slomkowski/octoglow/software/octoglowd2/src/main/kotlin/eu/slomkowski/octoglow/octoglowd/controller/FrontDisplayController.kt

package eu.slomkowski.octoglow.octoglowd.controller

import eu.slomkowski.octoglow.octoglowd.hardware.Hardware
import eu.slomkowski.octoglow.octoglowd.view.FrontDisplayView
import kotlinx.coroutines.channels.ticker
import kotlinx.coroutines.coroutineScope
import kotlinx.coroutines.launch
import mu.KLogging
import java.time.Duration
import java.time.LocalDateTime

class FrontDisplayController(
        private val hardware: Hardware,
        private val frontDisplayViews: List<FrontDisplayView>)
    : Controller(Duration.ofMillis(100)) {

    data class ViewInfo(
            val view: FrontDisplayView,
            var lastPooled: LocalDateTime?)

    companion object : KLogging() {
        fun updateViewIndex(current: Int, delta: Int, size: Int): Int {
            require(current in 0..(size - 1))
            return (10000 * size + current + delta) % size
        }
    }

    override suspend fun pool() = coroutineScope {
        require(frontDisplayViews.isNotEmpty())

        var currentViewIdx = 0
        val views = frontDisplayViews.map { ViewInfo(it, null) }

        hardware.frontDisplay.clear()

        for (t in ticker(100)) {

            val now = LocalDateTime.now()

            views.filter { it.lastPooled?.plus(it.view.getPreferredPoolingInterval())?.isBefore(now) ?: true }.forEach {
                it.view.poolStateUpdateAsync()
                it.lastPooled = now
            }

            val buttonReport = hardware.frontDisplay.getButtonReport()

            if (buttonReport.encoderDelta != 0) {
                logger.debug { "Encoder delta: ${buttonReport.encoderDelta}." }
            }

            val newViewIndex = updateViewIndex(currentViewIdx, buttonReport.encoderDelta, views.size)

            if (newViewIndex != currentViewIdx) {
                val newCurrentView = views[newViewIndex].view

                logger.debug { "Switched view to ${newCurrentView.name}." }

                launch {
                    hardware.frontDisplay.clear()
                    newCurrentView.redrawDisplay()
                }

                currentViewIdx = newViewIndex
            }
        }
    }

}
