slomkowski/octoglow/software/octoglowd/src/main/kotlin/eu/slomkowski/octoglow/octoglowd/hardware/Geiger.kt

package eu.slomkowski.octoglow.octoglowd.hardware

import io.github.oshai.kotlinlogging.KotlinLogging
import kotlin.time.Duration
import kotlin.time.Duration.Companion.milliseconds
import kotlin.time.Duration.Companion.seconds

enum class EyeDisplayMode {
    ANIMATION,
    FIXED_VALUE
}

enum class EyeInverterState {
    DISABLED,
    HEATING_LIMITED,
    HEATING_FULL,
    RUNNING
}

data class GeigerCounterState(
    val hasNewCycleStarted: Boolean,
    val hasCycleEverCompleted: Boolean,
    val numOfCountsInCurrentCycle: Int,
    val numOfCountsInPreviousCycle: Int,
    val currentCycleProgress: Duration,
    val cycleLength: Duration,
) {
    companion object {
        private val invalidBufferContent = intArrayOf(255, 255, 255, 255, 255, 255, 255, 255, 255, 255)

        const val SIZE_IN_BYTES = 11

        fun parse(buff: IntArray): GeigerCounterState {
            require(buff.size == SIZE_IN_BYTES) { "buffer size must be $SIZE_IN_BYTES" }

            check(!buff.sliceArray(1 until buff.size).contentEquals(invalidBufferContent)) { "read buffer has characteristic invalid pattern" }
            check(buff[1] == 2) { "invalid command identifier - expected 2 but got ${buff[1]}" }

            return GeigerCounterState(
                when (buff[2] and 0b1) {
                    1 -> true
                    else -> false
                },
                when (buff[2] and 0b10) {
                    0b10 -> true
                    else -> false
                },
                (buff[4] shl 8) + buff[3],
                (buff[6] shl 8) + buff[5],
                ((buff[8] shl 8) + buff[7]).seconds,
                ((buff[10] shl 8) + buff[9]).seconds
            )
        }
    }
}

data class GeigerDeviceState(
    val geigerVoltage: Double,
    val geigerPwmValue: Int,
    val eyeState: EyeInverterState,
    val eyeAnimationState: EyeDisplayMode,
    val eyeVoltage: Double,
    val eyePwmValue: Int,
) {
    companion object {
        private val invalidBufferContent = intArrayOf(255, 255, 255, 255, 255, 255, 255, 255, 255)

        const val SIZE_IN_BYTES = 10

        private const val GEIGER_ADC_SCALING_FACTOR: Double = 2.5 / 1024 / (4.7 / (4.7 + 4 * 470))

        private const val EYE_ADC_SCALING_FACTOR: Double = 2.5 / 1024 / (4.7 / (4.7 + 3 * 180))

        fun parse(buff: IntArray): GeigerDeviceState {
            require(buff.size == SIZE_IN_BYTES) { "buffer size must be $SIZE_IN_BYTES" }

            check(buff[1] == 1) { "invalid command identifier - expected 1 but got ${buff[1]}" }
            check(!buff.sliceArray(1 until buff.size).contentEquals(invalidBufferContent)) { "read buffer has characteristic invalid pattern" }

            val geigerAdcReadout = (buff[3] shl 8) + buff[2]
            val eyeAdcReadout = (buff[8] shl 8) + buff[7]

            return GeigerDeviceState(
                GEIGER_ADC_SCALING_FACTOR * geigerAdcReadout.toDouble(),
                buff[4],
                EyeInverterState.entries[buff[5]],
                EyeDisplayMode.entries[buff[6]],
                EYE_ADC_SCALING_FACTOR * eyeAdcReadout.toDouble(),
                buff[9],
            )
        }
    }

    init {
        require(geigerVoltage in 0.0..500.0) { "Geiger voltage must be between 0 V and 500 V, but was $geigerVoltage V" }
        require(eyeVoltage in 0.0..300.0) { "Eye voltage must be between 0 V and 300 V, but was $eyeVoltage V" }
    }
}

class Geiger(hardware: Hardware) : CustomI2cDevice(hardware, logger, 0x18, 5.milliseconds), HasBrightness {

    companion object {
        private val logger = KotlinLogging.logger {}

        private val CYCLE_MAX_DURATION: Duration = 0xffff.seconds

        internal const val ENTER_BOOTLOADER_COMMAND = 8
        internal val BOOTLOADER_MAGIC = "BOOT".map { it.code }.toIntArray()
        const val BOOTLOADER_I2C_ADDRESS = 0x19
    }

    override suspend fun initDevice() {
        // nothing to do
    }

    override suspend fun closeDevice() {
        setBrightness(3)
    }

    override suspend fun setBrightness(brightness: Int) {
        require(brightness in 0..MAX_BRIGHTNESS) { "brightness should be in range 0..$MAX_BRIGHTNESS" }
        sendCommand("set brightness", 7, brightness)
    }

    suspend fun getDeviceState(): GeigerDeviceState {
        val readBuffer = sendCommandAndReadData("get device state", GeigerDeviceState.SIZE_IN_BYTES, 1)
        return GeigerDeviceState.parse(readBuffer)
    }

    suspend fun getCounterState(): GeigerCounterState {
        val readBuffer = sendCommandAndReadData("get counter state", GeigerCounterState.SIZE_IN_BYTES, 2)
        return GeigerCounterState.parse(readBuffer)
    }

    suspend fun setCycleLength(duration: Duration) {
        require(duration > Duration.ZERO) { "duration has to be non-zero" }
        require(duration < CYCLE_MAX_DURATION) { "duration can be max $CYCLE_MAX_DURATION" }
        val seconds = duration.inWholeSeconds.toInt()

        sendCommand("set cycle length", 3, 0xff and seconds, 0xff and (seconds shr 8))
    }

    suspend fun reset() {
        sendCommand("reset", 4)
    }

    suspend fun setEyeConfiguration(enabled: Boolean, mode: EyeDisplayMode = EyeDisplayMode.ANIMATION) {
        logger.info { "Setting eye enabled: $enabled." }
        sendCommand(
            "set eye configuration",
            5, when (enabled) {
                true -> 1
                else -> 0
            }, mode.ordinal
        )
    }

    /**
     * Resets the device into the I2C bootloader (firmware/geiger/bootloader), 100 ms after the reply.
     * The bootloader listens on [BOOTLOADER_I2C_ADDRESS] for 1 s, then starts the application again.
     * Until then the device doesn't respond on its own address, the inverters are off.
     */
    suspend fun enterBootloader() {
        sendCommand("enter bootloader", ENTER_BOOTLOADER_COMMAND, *BOOTLOADER_MAGIC)
    }

    suspend fun setEyeValue(value: Int) {
        require(value in 0..255)
        sendCommand("set eye value", 6, value)
    }
}
