slomkowski/octoglow/software/octoglowd/src/main/kotlin/eu/slomkowski/octoglow/octoglowd/hardware/clockDisplay.kt

package eu.slomkowski.octoglow.octoglowd.hardware

import eu.slomkowski.octoglow.octoglowd.contentToBitString
import io.github.oshai.kotlinlogging.KotlinLogging

data class RemoteSensorReport(
    val sensorId: Int,
    val temperature: Double,
    val humidity: Double,
    val batteryIsWeak: Boolean,
    val alreadyReadFlag: Boolean,
    val manualTx: Boolean,
) {
    companion object {
        private val logger = KotlinLogging.logger {}

        private const val VALID_MEASUREMENT_FLAG = 1 shl 1
        private const val ALREADY_READ_FLAG = 1 shl 2

        fun toBitArray(i2CBuffer: IntArray) = BooleanArray(40).apply {
            for (i in 0..39) {
                this[i] = i2CBuffer[3 + i / 8] and (0b10000000 shr (i % 8)) != 0
            }
        }

        /**
         * This code is ported from https://www.chaosgeordend.nl/documents/analyse_rf433.py
         */
        fun calculateChecksum(i2CBuffer: IntArray): Boolean {
            var csum = 0x0
            var mask = 0xC
            val msg = toBitArray(i2CBuffer)
            val calculationBuffer = msg.copyOfRange(0, 8)
                .plus(msg.copyOfRange(36, 40))
                .plus(msg.copyOfRange(12, 36))

            val checksum = (i2CBuffer[4] shr 4) and 0xf

            for (b in calculationBuffer) {
                val bit = mask and 0x1
                mask = mask shr 1
                if (bit == 0x1) {
                    mask = mask xor 0x9
                }

                if (b) {
                    csum = csum xor mask
                }
            }

            csum = csum and 0xf

            return csum == checksum
        }

        fun parse(buff: IntArray): RemoteSensorReport? {
            require(buff.size == 8) { "invalid buffer length: ${buff.size}" }
            require(buff[1] == 4) { "invalid sensor report type: ${buff[1]}" }

            if ((buff[2] and VALID_MEASUREMENT_FLAG) == 0) {
                return null
            }

            val alreadyRead = (buff[2] and ALREADY_READ_FLAG) != 0

            val sensorId = buff[7] and 0b11
            val manualTx = (buff[4] and 0b1000) != 0
            val weakBattery = (buff[4] and 0b100) != 0

            val temperatureBits = (buff[5] shl 4) + ((buff[6] shr 4) and 0b1111)
            val temperature = (temperatureBits.toDouble() - 1220.0) * 1.0 / 18.0 + 0.0

            val humidity = 10.0 * (buff[6] and 0b1111) + ((buff[7] shr 4) and 0b1111)

            val areValuesValid = (sensorId in (1..3)) && (temperature in -40.0..60.0) && (humidity in 0.0..100.0)

            if (!areValuesValid) {
                return null
            }

            if (!calculateChecksum(buff)) {
                return null
            }

            if (!alreadyRead) {
                logger.trace {
                    String.format(
                        "ch=%d,temp=%2.1f,hum=%2.0f%%,wb=%b,tx=%b,raw=%s.",
                        sensorId,
                        temperature,
                        humidity,
                        weakBattery,
                        manualTx,
                        buff.contentToBitString().drop(18)
                    )
                }
            }

            return RemoteSensorReport(
                sensorId,
                temperature,
                humidity,
                weakBattery,
                alreadyRead,
                manualTx,
            )
        }
    }
}

class ClockDisplay(hardware: Hardware) : CustomI2cDevice(hardware, logger, 0x10), HasBrightness {

    companion object {
        private val logger = KotlinLogging.logger {}

        private const val UPPER_DOT: Int = 1 shl (14 % 8)
        private const val LOWER_DOT: Int = 1 shl (13 % 8)

        // must match firmware/clock-display/src/protocol.hpp and common/usi.hpp
        internal const val ENTER_BOOTLOADER_COMMAND = 7
        internal val BOOTLOADER_MAGIC = "BOOT".map { it.code }.toIntArray()
        const val BOOTLOADER_I2C_ADDRESS = 0x11
    }

    override suspend fun setBrightness(brightness: Int) {
        sendCommand("set brightness", 3, brightness)
    }

    override suspend fun initDevice() {
        // requires no init
    }

    override suspend fun closeDevice() {
        setBrightness(3)
        setRelays(relay1enabled = false, relay2enabled = false)
        sendCommand("set display to --:--", 1, 45, 45, 45, 45, UPPER_DOT or LOWER_DOT)
    }

    suspend fun retrieveRemoteSensorReport(): RemoteSensorReport? {
        val readBuffer = sendCommandAndReadData("get remote sensor report", 8, 4)
        return RemoteSensorReport.parse(readBuffer)
    }

    suspend fun retrieveLightSensorMeasurement(): Int {
        val readBuffer = sendCommandAndReadData("get light sensor measurement", 4, 5)
        // we invert sensor value, so a high amount of light is a high reading
        return (1023 - (readBuffer[2] + (readBuffer[3] shl 8))).also {
            check(it in 0..1023) { "Light sensor measurement $it is out of valid range 0..1023" }
        }
    }

    suspend fun setRelays(relay1enabled: Boolean, relay2enabled: Boolean) {
        sendCommand(
            "set relays",
            2,
            (if (relay1enabled) 0b01 else 0b00) or (if (relay2enabled) 0b10 else 0b00),
        )
    }

    /**
     * Resets the device into the I2C bootloader. The device replies, then resets via watchdog within 250 ms.
     * The bootloader listens on [BOOTLOADER_I2C_ADDRESS] for 1 s, then starts the application again.
     * Until then the device doesn't respond on its own address and the relays are off.
     * The firmware upload itself is done by [eu.slomkowski.octoglow.octoglowd.firmware.FirmwareBurner].
     */
    suspend fun enterBootloader() {
        sendCommand("enter bootloader", ENTER_BOOTLOADER_COMMAND, *BOOTLOADER_MAGIC)
    }

    suspend fun retrieveRelaysState(): Pair<Boolean, Boolean> {
        val readBuffer = sendCommandAndReadData("retrieve relays state", 3, 6)
        return Pair(
            (readBuffer[2] and 0b01) != 0,
            (readBuffer[2] and 0b10) != 0,
        )
    }

    private suspend fun setDisplay(
        hourTens: Char,
        hourOnes: Char,
        minuteTens: Char,
        secondTens: Char,
        upperDot: Boolean,
        lowerDot: Boolean
    ) {
        val dots = if (upperDot) {
            UPPER_DOT
        } else {
            0
        } or if (lowerDot) {
            LOWER_DOT
        } else {
            0
        }

        sendCommand(
            "set display",
            1,
            hourTens.code,
            hourOnes.code,
            minuteTens.code,
            secondTens.code,
            dots,
        )
    }

    suspend fun setFrontDisplayViewNumber(number: Int) {
        setDisplay(
            '-', '-',
            when (number < 10) {
                true -> ' '
                else -> (number / 10).digitToChar()
            },
            (number % 10).digitToChar(),
            upperDot = false,
            lowerDot = false,
        )
    }

    suspend fun setDisplay(hours: Int, minutes: Int, upperDot: Boolean, lowerDot: Boolean) {
        require(hours in 0..24)
        require(minutes in 0..60)

        setDisplay(
            when (hours < 10) {
                true -> ' '
                else -> (hours / 10).digitToChar()
            },
            (hours % 10).digitToChar(),
            (minutes / 10).digitToChar(),
            (minutes % 10).digitToChar(),
            upperDot,
            lowerDot
        )
    }
}
