slomkowski/octoglow/software/octoglowd/src/main/kotlin/eu/slomkowski/octoglow/octoglowd/hardware/Bme280.kt

package eu.slomkowski.octoglow.octoglowd.hardware

import eu.slomkowski.octoglow.octoglowd.trySeveralTimes
import io.github.oshai.kotlinlogging.KotlinLogging
import kotlinx.coroutines.coroutineScope
import kotlinx.coroutines.delay
import kotlinx.coroutines.withTimeout
import kotlin.math.exp

/**
 * Temperature in deg C, humidity in %, pressure in hPa.
 */
data class Bme280measurements(
    val temperature: Double,
    val humidity: Double,
    val realPressure: Double,
) {

    init {
        require(
            temperature in (-10.0..60.0)
                    && humidity in (0.0..100.0)
                    && realPressure in (900.0..1100.0)
        )
        { String.format("invalid report: %4.2f deg C, H: %3.0f%%, %4.0f hPa", temperature, humidity, realPressure) }
    }

    /**
     * Calculate mean sea-level pressure using elevation in meters.
     */
    fun getMeanSeaLevelPressure(elevation: Double): Double {
        require(elevation in 0.0..1000.0)

        val u = 0.0289644
        val g = 9.81
        val r = 8.3144598
        val tempK = temperature + 273.15

        val coeff = exp(-u * g * elevation / (r * tempK))

        return realPressure / coeff
    }

    companion object {
        /*
        This code was directly transplanted from
        https://github.com/ControlEverythingCommunity/BME280/blob/master/Java/BME280.java
         */
        fun parse(cd: CompensationData, adcP: Int, adcT: Int, adcH: Int): Bme280measurements {
            var var1 = (adcT.toDouble() / 16384.0 - cd.t1.toDouble() / 1024.0) * cd.t2.toDouble()
            var var2 =
                (adcT.toDouble() / 131072.0 - cd.t1.toDouble() / 8192.0) * (adcT.toDouble() / 131072.0 - cd.t1.toDouble() / 8192.0) * cd.t3.toDouble()
            val tFine = (var1 + var2).toLong().toDouble()
            val cTemp = (var1 + var2) / 5120.0

            var1 = tFine / 2.0 - 64000.0
            var2 = var1 * var1 * cd.p6.toDouble() / 32768.0
            var2 += var1 * cd.p5.toDouble() * 2.0
            var2 = var2 / 4.0 + cd.p4.toDouble() * 65536.0
            var1 = (cd.p3.toDouble() * var1 * var1 / 524288.0 + cd.p2.toDouble() * var1) / 524288.0
            var1 = (1.0 + var1 / 32768.0) * cd.p1.toDouble()
            var p = 1048576.0 - adcP.toDouble()
            p = (p - var2 / 4096.0) * 6250.0 / var1
            var1 = cd.p9.toDouble() * p * p / 2147483648.0
            var2 = p * cd.p8.toDouble() / 32768.0
            val pressure = (p + (var1 + var2 + cd.p7.toDouble()) / 16.0) / 100

            // Humidity offset calculations
            var varH = tFine - 76800.0
            varH =
                (adcH - (cd.h4 * 64.0 + cd.h5 / 16384.0 * varH)) * (cd.h2 / 65536.0 * (1.0 + cd.h6 / 67108864.0 * varH * (1.0 + cd.h3 / 67108864.0 * varH)))
            val humidity = varH * (1.0 - cd.h1 * varH / 524288.0)

            return Bme280measurements(cTemp, humidity, pressure)
        }
    }
}

data class CompensationData(
    val t1: Int,
    val t2: Int,
    val t3: Int,

    val p1: Int,
    val p2: Int,
    val p3: Int,
    val p4: Int,
    val p5: Int,
    val p6: Int,
    val p7: Int,
    val p8: Int,
    val p9: Int,

    val h1: Int,
    val h2: Int,
    val h3: Int,
    val h4: Int,
    val h5: Int,
    val h6: Int,
)

class Bme280(hardware: Hardware) : FactoryMadeI2cDevice(hardware, 0x76) {

    companion object {
        private val logger = KotlinLogging.logger {}

        private val uninitializedSensorReport = intArrayOf(128, 0, 0, 128, 0, 0, 128, 0)

        fun checkNot00andNotFF(list: IntArray) {

            check(!list.all { it == 0 }) { "data is all zeroes" }
            check(!list.all { it == 0xff }) { "data is all 0xff" }
        }

        fun toSignedShort(ba: IntArray, offset: Int): Int = toUnsignedShort(ba, offset).let { orig ->
            if (orig > 32767) {
                orig - 65536
            } else {
                orig
            }
        }

        fun toUnsignedShort(ba: IntArray, offset: Int): Int {
            val bYounger = ba[offset].apply { check(this in 0..255) { "young byte: $this" } }
            val bOlder = ba[offset + 1].apply { check(this in 0..255) { "old byte: $this" } }
            return bYounger + 256 * bOlder
        }

        /**
         * Sign-extends the [bitWidth]-bit two's-complement magnitude held in the low bits of this Int.
         * BME280 defines dig_H4/dig_H5 as signed 12-bit and dig_H6 as a signed 8-bit value.
         */
        fun Int.signExtend(bitWidth: Int): Int {
            val signBit = 1 shl (bitWidth - 1)
            return if (this and signBit != 0) this - (1 shl bitWidth) else this
        }
    }

    private var compensationData: CompensationData? = null

    override suspend fun initDevice() = coroutineScope {
        doWrite(0xe0, 0xb6)

        delay(100)

        doWrite(
            0xf2, 0b100,
            0xf5, 0b101_100_0_0,
            0xf4, 0b100_100_11
        )

        delay(100)

        val id = doTransaction(intArrayOf(0xd0), 1)[0]
        check(id == 0x60) { String.format("this is not BME280 chip, it has ID 0x%x", id) }

        withTimeout(2000) {
            while (isReadingCalibration()) {
                delay(100)
            }
        }

        val b1 = doTransaction(intArrayOf(0x88), 25)
        val b2 = doTransaction(intArrayOf(0xe1), 8)

        checkNot00andNotFF(b1)
        checkNot00andNotFF(b2)

        val c = CompensationData(
            t1 = toUnsignedShort(b1, 0),
            t2 = toSignedShort(b1, 2),
            t3 = toSignedShort(b1, 4),

            p1 = toUnsignedShort(b1, 6),
            p2 = toSignedShort(b1, 8),
            p3 = toSignedShort(b1, 10),
            p4 = toSignedShort(b1, 12),
            p5 = toSignedShort(b1, 14),
            p6 = toSignedShort(b1, 16),
            p7 = toSignedShort(b1, 18),
            p8 = toSignedShort(b1, 20),
            p9 = toSignedShort(b1, 22),

            h1 = b1[24],
            h2 = toSignedShort(b2, 0),
            h3 = b2[2],
            h4 = ((b2[3] shl 4) + (b2[4] and 0x0f)).signExtend(12),
            h5 = (((b2[4] shr 4) and 0x0f) + (b2[5] shl 4)).signExtend(12),
            h6 = b2[7].signExtend(8)
        )

        logger.debug { "Compensation data: $c." }

        compensationData = c
    }

    override suspend fun closeDevice() {
        // nothing to do
    }

    private suspend fun isReadingCalibration(): Boolean = doTransaction(intArrayOf(0xf3), 1)[0] and 0x1 != 0

    suspend fun readReport(): Bme280measurements = trySeveralTimes(3, logger, "read BME280 report") {
        val buf = doTransaction(intArrayOf(0xf7), 8)

        check(!buf.contentEquals(uninitializedSensorReport)) { "sensor is not initialized" }

        val adcP = buf[0] shl 12 or (buf[1] shl 4) or (buf[2] shr 4)
        val adcT = buf[3] shl 12 or (buf[4] shl 4) or (buf[5] shr 4)
        val adcH = buf[6] shl 8 or buf[7]

        logger.trace { "adcP: $adcP, adcT: $adcT, adcH: $adcH." }

        Bme280measurements.parse(checkNotNull(compensationData) { "sensor is not initialized" }, adcP, adcT, adcH)
    }
}
