slomkowski/octoglow/firmware/geiger/msp430/i2c-slave_hd.cpp

#include "i2c-slave.hpp"
#include "magiceye.hpp"
#include "inverter.hpp"

#include <msp430.h>

#define SDA_PIN BIT7
#define SCL_PIN BIT6

using namespace octoglow::geiger;

void i2c::setClockToHigh() {
    BCSCTL1 = XT2OFF | XTS | DIVA_2 | (0x0f & CALBC1_16MHZ);
    DCOCTL = CALDCO_16MHZ;
}

void i2c::setClockToLow() {
    BCSCTL1 = XT2OFF | XTS | DIVA_2 | (0x0f & CALBC1_8MHZ);
    DCOCTL = CALDCO_8MHZ;
}

void i2c::init() {
    P1SEL |= SDA_PIN + SCL_PIN; // Assign I2C pins to USCI_B0
    P1SEL2 |= SDA_PIN + SCL_PIN; // Assign I2C pins to USCI_B0
    UCB0CTL1 |= UCSWRST; // Enable SW reset
    UCB0CTL0 = UCMODE_3 + UCSYNC; // I2C Slave, synchronous mode
    UCB0I2COA = SLAVE_ADDRESS; // set own (slave) address
    UCB0CTL1 &= ~UCSWRST; // Clear SW reset, resume operation
    IE2 |= UCB0TXIE + UCB0RXIE; // Enable TX and RX interrupt
    UCB0I2CIE |= UCSTTIE + UCSTPIE; // Enable interrupt on I2C start
}

/**
 * Interrupt called on both send and receive data. TI's naming is confusing.
 */
__interrupt_vec(USCIAB0TX_VECTOR) void USCIAB0TX_ISR() {
    if (IFG2 & UCB0TXIFG) {
        i2c::onTransmit(&UCB0TXBUF);
    } else if (IFG2 & UCB0RXIFG) {
        i2c::onReceive(UCB0RXBUF);
    }
}

/**
 * State machine interrupt. Called on I2C start, stop, nack etc. TI's naming is confusing.
 * STOP of the previous transmission and START of the next one may both be pending, STOP is older.
 * Each flag is cleared before it's handled, so a flag set meanwhile isn't lost.
 */
__interrupt_vec(USCIAB0RX_VECTOR) void USCIAB0RX_ISR() {
    if (UCB0STAT & UCSTPIFG) {
        UCB0STAT &= ~UCSTPIFG;
        i2c::onStop();
    }

    if (UCB0STAT & UCSTTIFG) {
        UCB0STAT &= ~UCSTTIFG;
        i2c::onStart();
    }

    UCB0STAT &= ~(UCNACKIFG + UCALIFG);
}

volatile protocol::DeviceState &i2c::hd::getDeviceState() {
    static volatile protocol::DeviceState state;

    state.eyeState = magiceye::state;
    state.eyeAnimationMode = magiceye::animationMode;
    state.eyePwmValue = TA1CCR1;
    state.geigerPwmValue = TA0CCR1;
    state.geigerVoltage = inverter::geigerAdcReadout;
    state.eyeVoltage = inverter::eyeAdcReadout;

    return state;
}
