slomkowski/octoglow/firmware/geiger/noarch/magiceye.cpp

#include "main.hpp"
#include "magiceye.hpp"
#include "inverter.hpp"
#include "geiger-counter.hpp"
#include "animation.hpp"

constexpr uint16_t PREHEAT_TIME_SECONDS = 8;
constexpr uint16_t POSTHEAT_TIME_SECONDS = 5;
constexpr uint16_t MAX_SECONDS_WITHOUT_PREHEAT = 5;

using namespace octoglow::geiger;
using namespace octoglow::geiger::magiceye;
using namespace octoglow::geiger::protocol;

namespace octoglow::geiger::magiceye {
    volatile EyeInverterState state = EyeInverterState::DISABLED;
    volatile EyeDisplayMode animationMode = EyeDisplayMode::ANIMATION;
}

static uint16_t cyclesCounter = UINT16_MAX;

void magiceye::tick() {
    if (state == EyeInverterState::HEATING_LIMITED and cyclesCounter >= PREHEAT_TIME_SECONDS * TICK_TIMER_FREQ) {
        hd::enableHeater2(true);
        state = EyeInverterState::HEATING_FULL;
        cyclesCounter = 0;
    } else if (state == EyeInverterState::HEATING_FULL and cyclesCounter >= POSTHEAT_TIME_SECONDS * TICK_TIMER_FREQ) {
        state = EyeInverterState::RUNNING;
        cyclesCounter = 0;
        inverter::setEyeEnabled(true);
    }

    if (cyclesCounter != UINT16_MAX) {
        ++cyclesCounter;
    }

    if (animationMode == EyeDisplayMode::ANIMATION) {
        static uint16_t previousValue = UINT16_MAX;
        geiger_counter::updateGeigerState();
        const uint16_t currentValue = geiger_counter::geigerState.numOfCountsCurrentCycle;

        setDacOutputValue(_animate(currentValue > previousValue));

        previousValue = currentValue;
    }
}

void magiceye::setEnabled(const bool enabled) {
    if (enabled and state == EyeInverterState::DISABLED) {
        if (cyclesCounter < MAX_SECONDS_WITHOUT_PREHEAT * TICK_TIMER_FREQ) {
            hd::enableHeater1(true);
            hd::enableHeater2(true);
            state = EyeInverterState::HEATING_FULL;
        } else {
            hd::enableHeater1(true);
            state = EyeInverterState::HEATING_LIMITED;
        }
        cyclesCounter = 0;
    } else if (!enabled and state != EyeInverterState::DISABLED) {
        inverter::setEyeEnabled(false);
        state = EyeInverterState::DISABLED;
        cyclesCounter = 0;
        hd::enableHeater1(false);
        hd::enableHeater2(false);
    }
}

void magiceye::configure(const volatile EyeConfiguration &configuration) {
    setEnabled(configuration.enabled);
    animationMode = configuration.mode;
}
