slomkowski/octoglow/software/octoglowd/src/test/kotlin/eu/slomkowski/octoglow/octoglowd/hardware/GeigerTest.kt

package eu.slomkowski.octoglow.octoglowd.hardware

import eu.slomkowski.octoglow.octoglowd.hardware.mock.HardwareMock
import io.github.oshai.kotlinlogging.KotlinLogging
import kotlinx.coroutines.delay
import kotlinx.coroutines.runBlocking
import org.assertj.core.api.Assertions.assertThat
import org.assertj.core.api.Assertions.assertThatThrownBy
import org.junit.jupiter.api.Tag
import org.junit.jupiter.api.Test
import org.junit.jupiter.api.extension.ExtendWith
import kotlin.math.sqrt
import kotlin.time.Duration
import kotlin.time.Duration.Companion.milliseconds
import kotlin.time.Duration.Companion.minutes
import kotlin.time.Duration.Companion.seconds


@Tag("hardware")
@ExtendWith(HardwareParameterResolver::class)
class GeigerTest {

    companion object {
        private val logger = KotlinLogging.logger {}
    }

    @Test
    fun testGeigerCounterStateParse() {
        assertThat(GeigerCounterState.parse(intArrayOf(255, 2, 0, 23, 0, 32, 0, 50, 0, 200, 0))).isEqualTo(
            GeigerCounterState(
                hasNewCycleStarted = false,
                hasCycleEverCompleted = false,
                numOfCountsInCurrentCycle = 23,
                numOfCountsInPreviousCycle = 32,
                currentCycleProgress = 50.seconds,
                cycleLength = 200.seconds,
            )
        )

        assertThat(GeigerCounterState.parse(intArrayOf(255, 2, 3, 23, 0, 92, 0, 50, 0, 44, 1))).isEqualTo(
            GeigerCounterState(
                hasNewCycleStarted = true,
                hasCycleEverCompleted = true,
                numOfCountsInCurrentCycle = 23,
                numOfCountsInPreviousCycle = 92,
                currentCycleProgress = 50.seconds,
                cycleLength = 5.minutes,
            )
        )

        assertThatThrownBy {
            val invalid = intArrayOf(0, 255, 255, 255, 255, 255, 255, 255, 255)
            GeigerCounterState.parse(invalid)
        }
    }

    @Test
    fun testGeigerDeviceStateParse() {
        // buff layout: [_, cmd=1, adcLo, adcHi, geigerPwm, eyeState, eyeAnim, eyeAdcLo, eyeAdcHi, eyePwm]
        val state = GeigerDeviceState.parse(intArrayOf(0, 1, 100, 1, 42, 3, 1, 50, 1, 77))

        assertThat(state.geigerPwmValue).isEqualTo(42)
        assertThat(state.eyeState).isEqualTo(EyeInverterState.RUNNING)
        assertThat(state.eyeAnimationState).isEqualTo(EyeDisplayMode.FIXED_VALUE)
        // eyePwmValue must come from buff[9] (77), not from buff[8] (1, the eye-ADC high byte)
        assertThat(state.eyePwmValue).isEqualTo(77)
    }

    @Test
    fun testSetBrightnessRejectsOutOfRange(): Unit = runBlocking {
        val geiger = Geiger(HardwareMock())
        assertThatThrownBy { runBlocking { geiger.setBrightness(-1) } }
            .isInstanceOf(IllegalArgumentException::class.java)
        assertThatThrownBy { runBlocking { geiger.setBrightness(MAX_BRIGHTNESS + 1) } }
            .isInstanceOf(IllegalArgumentException::class.java)
    }

    @Test
    fun testSetCycleLengthRejectsOutOfRange(): Unit = runBlocking {
        val geiger = Geiger(HardwareMock())
        assertThatThrownBy { runBlocking { geiger.setCycleLength(Duration.ZERO) } }
            .isInstanceOf(IllegalArgumentException::class.java)
        assertThatThrownBy { runBlocking { geiger.setCycleLength(0x10000.seconds) } }
            .isInstanceOf(IllegalArgumentException::class.java)
    }

    @Test
    fun testResetAndSetCycleLength(hardware: Hardware): Unit = runBlocking {
        hardware.geiger.reset()
        hardware.geiger.getCounterState().apply {
            assertThat(hasCycleEverCompleted).isFalse()
            assertThat(numOfCountsInCurrentCycle).isZero()
        }

        val testLength = 138.seconds
        hardware.geiger.setCycleLength(testLength)

        hardware.geiger.getCounterState().apply {
            assertThat(cycleLength).isEqualTo(testLength)
        }

        hardware.geiger.setCycleLength(5.minutes)
        hardware.geiger.getCounterState().apply {
            assertThat(cycleLength).isEqualTo(5.minutes)
        }
    }

    @Test
    @Tag("hardware-geiger-eye")
    fun testSetBrightnessTo1(hardware: Hardware): Unit = runBlocking {
        hardware.geiger.setBrightness(1) // 110
    }

    @Test
    @Tag("hardware-geiger-eye")
    fun testSetBrightnessTo2(hardware: Hardware): Unit = runBlocking {
        hardware.geiger.setBrightness(2) // 140
    }

    @Test
    @Tag("hardware-geiger-eye")
    fun testSetBrightnessTo3(hardware: Hardware): Unit = runBlocking {
        hardware.geiger.setBrightness(3) // 180
    }

    @Test
    @Tag("hardware-geiger-eye")
    fun testSetBrightnessTo4(hardware: Hardware): Unit = runBlocking {
        hardware.geiger.setBrightness(4) // 210
    }

    @Test
    @Tag("hardware-geiger-eye")
    fun testSetBrightnessTo5(hardware: Hardware): Unit = runBlocking {
        hardware.geiger.setBrightness(5) // 250
    }

    @Test
    @Tag("hardware-geiger-eye")
    fun testGeigerVoltage(hardware: Hardware): Unit = runBlocking {
        val voltages = mutableListOf<Double>()

        repeat(10) {
            val voltage = hardware.geiger.getDeviceState().geigerVoltage
            voltages.add(voltage)
            delay(100.milliseconds)
        }
        logger.info { "Measured voltages: $voltages" }
        assertThat(voltages.average()).isBetween(380.0, 420.0)
    }

    @Test
    fun testSetBrightness(hardware: Hardware): Unit = runBlocking {
        for (i in 0..5) {
            logger.info { "Setting brightness to $i." }
            hardware.geiger.setBrightness(i)
            delay(10_000)
        }

        hardware.geiger.setBrightness(3)
    }

    @Test
    fun testGetCounterState(hardware: Hardware): Unit = runBlocking {
        //geiger.reset()

        repeat(50) {
            val state = hardware.geiger.getCounterState()
            logger.info { "State: $state." }
            delay(50)
        }
    }

    @Test
    @Tag("hardware-geiger-eye")
    fun testEyeVoltages(hardware: Hardware): Unit = runBlocking {
        hardware.geiger.setEyeConfiguration(true)
        val voltages = listOf(110.0, 140.0, 180.0, 210.0, 250.0)

        voltages.forEachIndexed { index, voltage ->
            hardware.geiger.setBrightness(index + 1)
            delay(4.seconds)

            val voltageValues = (0..30).map {
                delay(50.milliseconds)
                hardware.geiger.getDeviceState().eyeVoltage
            }
            val valuesAvg = voltageValues.average()

            logger.info {
                "Voltage: $voltage V, avg measured: ${String.format("%.1f", valuesAvg)} V, diff: ${String.format("%.1f", valuesAvg - voltage)} V st dev: ${
                    String.format(
                        "%.1f",
                        voltageValues.standardDeviation()
                    )
                }."
            }
        }
    }

    @Test
    fun testGetDeviceState(hardware: Hardware): Unit = runBlocking {

//        hardware.geiger.reset()

        repeat(50) {
            val state = hardware.geiger.getDeviceState()
            logger.info { "State: $state." }
            delay(80)
        }
    }

    @Test
    @Tag("hardware-geiger-eye")
    fun enableEye(hardware: Hardware) {
        setEye(hardware, true)
    }

    @Test
    @Tag("hardware-geiger-eye")
    fun disableEye(hardware: Hardware) {
        setEye(hardware, false)
    }

    private fun setEye(hardware: Hardware, v: Boolean) = runBlocking {
        hardware.geiger.setEyeConfiguration(v)
    }


    @Test
    @Tag("hardware-geiger-eye")
    fun testEye(hardware: Hardware): Unit = runBlocking {
        val geiger = hardware.geiger
        geiger.setEyeConfiguration(false)
        geiger.getDeviceState().apply {
            assertThat(eyeState).isEqualTo(EyeInverterState.DISABLED)
        }

        geiger.setEyeConfiguration(true, EyeDisplayMode.ANIMATION)
        geiger.getDeviceState().apply {
            assertThat(eyeState).isEqualTo(EyeInverterState.HEATING_LIMITED)
            assertThat(eyeAnimationState).isEqualTo(EyeDisplayMode.ANIMATION)
        }

        delay(1000)

        geiger.getDeviceState().apply {
            assertThat(eyeState).isEqualTo(EyeInverterState.HEATING_LIMITED)
            assertThat(eyeAnimationState).isEqualTo(EyeDisplayMode.ANIMATION)
        }

        delay(8000)

        geiger.getDeviceState().apply {
            assertThat(eyeState).isEqualTo(EyeInverterState.HEATING_FULL)
            assertThat(eyeAnimationState).isEqualTo(EyeDisplayMode.ANIMATION)
        }

        delay(5000)

        geiger.getDeviceState().apply {
            assertThat(eyeAnimationState).isEqualTo(EyeDisplayMode.ANIMATION)
            assertThat(eyeState).isEqualTo(EyeInverterState.RUNNING)
        }

        delay(2000)

        geiger.getDeviceState().also {
            logger.info { "State: $it." }
        }

        geiger.setEyeConfiguration(true, EyeDisplayMode.FIXED_VALUE)
        geiger.getDeviceState().apply {
            assertThat(eyeState).isEqualTo(EyeInverterState.RUNNING)
            assertThat(eyeAnimationState).isEqualTo(EyeDisplayMode.FIXED_VALUE)
        }
        for (i in 0..15) {
            geiger.setEyeValue(10 * i)
            delay(1000)
        }

        for (i in 0..5) {
            geiger.setBrightness(i)
            delay(1000)
        }

        geiger.setEyeConfiguration(true, EyeDisplayMode.ANIMATION)
        geiger.setBrightness(3)
        geiger.getDeviceState().apply {
            assertThat(eyeState).isEqualTo(EyeInverterState.RUNNING)
            assertThat(eyeAnimationState).isEqualTo(EyeDisplayMode.ANIMATION)
        }

        geiger.setEyeConfiguration(false)
        geiger.getDeviceState().apply {
            assertThat(eyeState).isEqualTo(EyeInverterState.DISABLED)
            assertThat(eyeAnimationState).isEqualTo(EyeDisplayMode.ANIMATION)
        }
    }

    private fun List<Double>.standardDeviation(): Double {
        val mean = average()
        return sqrt(sumOf { (it - mean) * (it - mean) } / size)
    }
}
