slomkowski/octoglow/firmware/front-display/test/stubs.cpp

#include "stubs.hpp"

#include "clock.hpp"
#include "display.hpp"
#include "flash.hpp"
#include "eeprom.hpp"
#include "encoder.hpp"
#include "i2c-slave.hpp"
#include "main.hpp"

#include <cstring>

using namespace octoglow::front_display;

int test::displayPoolCalls = 0;

uint8_t test::milliseconds = 0;

uint8_t test::endYearOfConstruction = 77;

uint8_t test::flash[FLASH_SIZE];

int test::flashPageWrites = 0;

uint8_t clock::milliseconds() {
    return test::milliseconds;
}

void display::hd::displayPool() {
    ++test::displayPoolCalls;
}

int8_t encoder::getValueAndClear() {
    const auto v = _currentEncoderSteps;
    _currentEncoderSteps = 0;
    return v;
}

encoder::ButtonState encoder::getButtonStateAndClear() {
    const auto v = _currentButtonState;
    _currentButtonState = ButtonState::NO_CHANGE;
    return v;
}

uint8_t eeprom::readEndYearOfConstruction() {
    return test::endYearOfConstruction;
}

void eeprom::saveEndYearOfConstruction(const uint8_t year) {
    test::endYearOfConstruction = year;
}

// the same algorithm as _crc8_ccitt_update() from avr-libc
uint8_t i2c::crc8ccittUpdate(const uint8_t inCrc, const uint8_t inData) {
    uint8_t data = inCrc ^ inData;
    for (int i = 0; i < 8; i++) {
        if ((data & 0x80) != 0) {
            data <<= 1;
            data ^= 0x07;
        } else {
            data <<= 1;
        }
    }
    return data;
}

void bootloader::flash::writePage(const uint16_t address, const uint8_t *const data) {
    ++test::flashPageWrites;
    memcpy(test::flash + address, data, SPM_PAGESIZE);
}

uint8_t bootloader::flash::readByte(const uint16_t address) {
    return test::flash[address];
}
