slomkowski/octoglow/software/octoglowd2/src/test/kotlin/eu/slomkowski/octoglow/FrontDisplayTest.kt

package eu.slomkowski.octoglow

import io.dvlopt.linux.i2c.I2CBus
import kotlinx.coroutines.delay
import kotlinx.coroutines.runBlocking
import mu.KLogging
import org.junit.jupiter.api.Test
import org.junit.jupiter.api.extension.ExtendWith
import kotlin.system.measureTimeMillis
import kotlin.test.assertEquals

@ExtendWith(I2CBusParameterResolver::class)
class FrontDisplayTest {

    companion object : KLogging()

    @Test
    fun testSetUpperBar(i2CBus: I2CBus) {
        runBlocking {
            val frontDisplay = FrontDisplay(i2CBus)

            (0..19).forEach {
                frontDisplay.setUpperBar(listOf(it))
                delay(100)
            }

            frontDisplay.setUpperBar(arrayOf(
                    true, true, false, true, false,
                    false, false, false, false, false,
                    false, false, true, false, false,
                    false, false, false, false, true))

            delay(1000)

            frontDisplay.setUpperBar(listOf(0, 1, 19))

            delay(1000)

            frontDisplay.setUpperBar(listOf(0, 1, 19), true)
        }
    }

    @Test
    fun testSetStaticText(i2CBus: I2CBus) {
        runBlocking {
            FrontDisplay(i2CBus).apply {
                clear()
                setStaticText(0, "Foo bar text.")
                delay(1000)

                val t = measureTimeMillis {
                    setStaticText(1, "Znajdź pchły, wróżko! Film \"Teść\".")
                }
                logger.info { "Executed in $t ms." }
            }
        }
    }

    @Test
    fun testSetScrollingText(i2CBus: I2CBus) {
        runBlocking {
            FrontDisplay(i2CBus).apply {
                clear()
                setScrollingText(Slot.SLOT0, 34, 5,
                        "The quick brown fox jumps over the lazy dog. 20\u00B0C Dość gróźb fuzją, klnę, pych i małżeństw!")
            }
        }
    }

    @Test
    fun testGetButtonReport(i2CBus: I2CBus) {
        runBlocking {
            FrontDisplay(i2CBus).apply {
                val report1 = getButtonReport()
                logger.info("Buttons 1: {}", report1)
                val report2 = getButtonReport()
                logger.info("Buttons 2: {}", report2)

                assertEquals(ButtonState.NO_CHANGE, report2.button)
                assertEquals(0, report2.encoderDelta)
            }
        }
    }

    @Test
    fun testCharts(i2CBus: I2CBus) {
        runBlocking {
            FrontDisplay(i2CBus).apply {
                clear()
                setOneLineDiffChart(5 * 23, listOf(0, 1, 2, 3, 4, 5, 6, 7, 6, 5, 4), 1)
                setOneLineDiffChart(5 * 26, listOf(16.0, 21.0, 84.3, 152.0, 79.6, 61.3, 68.2), 31.5)
                setTwoLinesDiffChart(5 * 13, listOf(0, 2, 4, 6, 8, 10, 12, 14, 16, 18, 20, 22, 24, 26, 28, 26, 24, 22, 20, 18, 16, 14, 14), 2)
            }
        }
    }
}
